Assane401/Task1-Linear-Voltage-Regulator/schema_ltspice.asc

C1: polcap; 100µ; V=6.3 Irms=0 Rser=0.9 Lser=0 mfg="AVX" pn="TAJD107M006" type="Tantalum"
C2: polcap; 330n; V=6.3 Irms=0 Rser=0.9 Lser=0
C3: polcap; 10µ; V=6.3 Irms=0 Rser=4 Lser=0 mfg="AVX" pn="TAJA106M006" type="Tantalum"
U1: LT1085-5
V1: voltage; SINE(12 0.5 100)
Named nets: 0, Vout, Vin
.tran 0 100m 0 0.01m
