Assane401/Task1-Linear-Voltage-Regulator/schema_ltspice_reponse_charge.asc

C1: polcap; 100µ; V=6.3 Irms=0 Rser=0.9 Lser=0 mfg="AVX" pn="TAJD107M006" type="Tantalum"
C2: polcap; 330n; V=6.3 Irms=0 Rser=0.9 Lser=0
C3: polcap; 10µ; V=6.3 Irms=0 Rser=4 Lser=0
D1: LED
I1: current; PULSE(0.05 0.5 10m 1u 1u 20m 40m)
R1: res; 150
U1: LT1085-5
V1: voltage; SINE(12 0.5 100)
Named nets: 0, Vout, Vin
.tran 0 80m 0 0.01m
